GregorySchock/Velostat-Dance-Game-Sensors/velostat holder/top.stl

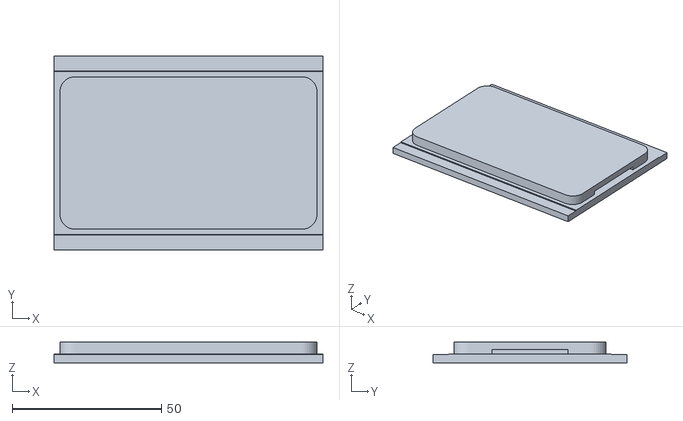
[picture p15: CAD file, 2020-06-27]
velostat holder/top.stl
90.0 x 65.0 x 7.00
